INgoRah/IN10d/src/OwDevices.cpp

/* LICENSE
 *
 */
/*
 * Includes
 */
#include "Arduino.h"			 // for delayMicroseconds, digitalPinToBitMask, etc
#include <avr/pgmspace.h>
#include <avr/wdt.h>
#include "DS2482.h"
#include "OwDevices.h"

/*
 * Library class includes
 */

/*
 * Local constants
 */
#define READSCRATCH     0xBE  // Read from scratchpad
#define WRITESCRATCH    0x4E  // Write to scratchpad
#define STARTCONVO      0x44  // Tells device to take a temperature reading and put it on the scratchpad
// Scratchpad locations
#define TEMP_LSB        0
#define TEMP_MSB        1
#define HIGH_ALARM_TEMP 2
#define LOW_ALARM_TEMP  3

#if defined(AVRSIM)
uint8_t	pio_data[0x0f];
#endif

void adrGen(byte adr[8], uint8_t id);

/*
 * Objects
 */

/*
 * Local variables
 */

/*
* Function declarations
*/
void OwDevices::begin(OneWireBase *ds)
{
	ow = ds;
	ow->resetDev();
	ow->configureDev(DS2482_CONFIG_APU);
	for (int i = 0; i < MAX_BUS; i++) {
		// search devs
		for (int j = 0; j < MAX_ADR; j++) {
			pio_data[i][j] = 0xff;
			dev_vers[i][j] = 0;
		}
	}
}

void OwDevices::cacheInit()
{
	uint8_t adr[8];
	byte _data[MAX_CFG_SIZE];

	if (debug > 0) {
		Serial.println(F("Cache and Version update"));
	}
	for (int i = 0; i < MAX_BUS; i++) {
		ow->selectChannel(i);
		ow->reset_search();
		// search devs
		while (ow->search(adr)) {
			wdt_reset();
			if (adr[0] == 0x29) {
				ds2408PioGet(i, adr, true);
				if (adr[1] < MAX_ADR) {
					dev_vers[i][adr[1]] = 5;
					if (debug > 0) {
						Serial.print(i, HEX);
						Serial.print(F("."));
						Serial.println(adr[1], HEX);
					}
					ds2408CfgRead(i, adr, _data);
					dev_vers[i][adr[1]] = _data[22];
				}
			}
		}
	}
	//versionUpdate(0, 8);
	//versionUpdate(0, 2);
}

void OwDevices::adrGen(uint8_t bus, uint8_t adr[8], uint8_t id)
{
	adr[1] = id; // id selector
	adr[2] = bus;
	adr[3] = (uint8_t)~id;
	adr[4] = (uint8_t)~bus;
	if (adr[0] != 0x28 && adr[0] != 0x20) {
		/* set me up */
		adr[0] = 0x29; // type
	}
	adr[5] = 0x66;
	adr[6] = 0x77;
	adr[7] = ow->crc8 (adr, 7);
}

/* version 2 does not support long press detection
   version 7 supports own timer a dimming  via spécial 
   command C5 */
uint8_t OwDevices::getVersion(uint8_t bus, uint8_t id)
{
	return dev_vers[bus][id];
}

void OwDevices::versionUpdate(uint8_t bus, uint8_t id)
{
	byte adr[8], _data[MAX_CFG_SIZE];

	if (dev_vers[bus][id] == 0)
		/* not found */
		return;
	adrGen(bus, adr, id);
	ds2408CfgRead(bus, adr, _data);
	dev_vers[bus][id] = _data[22];
	wdt_reset();
	if (debug > 1) {
		Serial.print(bus);
		Serial.print(".");
		Serial.print(id);
		Serial.print(F(" version = "));
		Serial.println(dev_vers[bus][id]);
	}
}

/* requires bus selected already before */
uint8_t OwDevices::ds2408LatchReset(uint8_t* addr)
{
	uint8_t retry, tmp, err = 0;
	bool res;

#if defined(AVRSIM)
	return 0xAA;
#endif
	retry = LATCH_RESET_RETRY - 1;
	do {
		tmp = 0xff;
		res = ow->reset();
		if (res && ow->last_err == 0)
			ow->select(addr);
		if (ow->last_err == 0)
			ow->write (0xC3);
		if (ow->last_err == 0)
			tmp = ow->read();
		if (tmp == 0xAA)
			break;
		if (ow->last_err != 0) {
			err = ow->last_err;
		}
		if (err == 0)
			err = ow->last_err;
		delay(LATCH_RESET_RETRY - retry);
	} while (--retry > 0);
#ifdef DEBUG
	if ((err && retry == 0) || (err && debug > 0)) {
		log_time();
		Serial.print (F("latch reset err="));
		Serial.print (err);
		if (retry == 0)
			Serial.println(F(" ERR! "));
		else {
			Serial.print(F(" retry="));
			Serial.println(retry);
		}
	}
#endif
	if (retry == 0)
		return 0xff;

	return tmp;
}

/* Read DS2408 registers
 * [0] PIO Logic State
 * [1] Output latch
 * [2] Activity latch state
 * [3] Conditional search channel selection (unused)
 * [4] Conditional search polarity selection (unused)
 * [5] Status
 * [6] Status ext 1, used for press time detection
 * [7] Status ext 2
 *
 * Returns 0xaa in case of successful read and latch reset
 * Returns 0xff in case of latch reset issue
 * Returns 0 in case of bus error or timeout -> to be repeated
 * */
uint8_t OwDevices::ds2408RegRead(byte bus, uint8_t* addr, uint8_t* data, bool latch_reset)
{
	bool ret;
	uint8_t tmp, err = 0;
	uint8_t buf[3];  // Put everything in the buffer so we can compute CRC easily.

#if defined(AVRSIM)
	data[1] = 0x55;
	return 0xAA;
#endif
	uint8_t retry = REG_RETRY - 1;

	// read data registers
	buf[0] = 0xF0;    // Read PIO Registers
	buf[1] = 0x88;    // LSB address
	buf[2] = 0x00;    // MSB address
	do {
		//wdt_reset(); ??
		/* read latch */
		ret = ow->selectChannel(bus);
		if (ow->last_err == 0)
			ret = ow->reset();
		if (ret && ow->last_err == 0)
			ow->select(addr);
		if (ow->last_err == 0)
			ow->write (buf, 3);
		// 3 cmd bytes, 6 data bytes, 2 0xFF, 2 CRC16
		// 1:
		// try this: alway read not running into a watchdog
		// on the slave
		// if (ow->last_err == 0)
			ow->read (data, 10);
		/* check for valid status register */
		if (data[5] != 0xff)
			break;
		if (err == 0)
			err = ow->last_err;
		// if we got here, there is an issue and we
		// will try again
		delay(5);
	} while (--retry > 0);
	if (err) {
#ifdef DEBUG
		if (debug > 0  || retry == 0) {
			log_time();
			Serial.print(F("RegRead err="));
			Serial.print(err);
			if (retry == 0)
				Serial.println(F("ERR! "));
			else {
				Serial.print(F(" retry="));
				Serial.println(retry);
			}
		}
#endif
		if ((retry == 0 || data[5] == 0xff) && !latch_reset)
			return 0xff;
	}
	// TODO update cache here?
	pio_data[bus][addr[1] & 0x0f] = data[1];
	// clear the alarm status
	tmp = ds2408LatchReset(addr);

	return tmp;
}

/* Send channel data - currently not used */
uint8_t OwDevices::ds2408ChWrite(byte bus, uint8_t* addr, uint8_t* data, int cnt)
{
	(void)bus;
	(void)addr;
	(void)data;
	(void)cnt;
#if 0
	uint8_t r;
	int i;

	ow->selectChannel(bus);
	ow->reset();
	ow->select(addr);
	ow->write (0x5A);
	for (i = 0; i < cnt; i++) {
		ow->write (data[i]);
		r = ow->read();
		if (r != 0xAA) {
			// should be data[i] ... but the implementation seems wrong
			Serial.print(r, HEX);
		}
	}
#endif
	return 0xaa;
}

void OwDevices::toggleDs2413(byte bus, uint8_t* addr)
{
#if 0
	unsigned char pio, pion;
	int cnt = 10;

	ow->selectChannel(bus);
	do {
		ow->reset();
		ow->select(addr);
		ow->write (0xF5);
		pio = ow->read();
		if (cnt-- == 0)
			return;
	} while (((pio & 0xF) != (~(pio >> 4) & 0xF)));
	if ((pio & 2) == 0)
		pion = 3;
	else
		pion = 2;
	pion |= 0x2;
	cnt = 10;
	do {
		ow->reset();
		ow->select(addr);
		ow->write (0x5A);
		ow->write (0xFC | pion);
		ow->write (0xFF & (~(0xFC | pion)));
		pio = ow->read();
		if (cnt-- == 0)
			return;
	} while (pio != 0xAA);
#else
	(void)bus;
	(void)addr;
#endif
}

uint8_t OwDevices::ds2408PioSet(byte bus, uint8_t* addr, uint8_t pio)
{
#if defined(AVRSIM_TOP)
	pio_data[bus][addr[1] & 0x0f] = pio;
	return 0xAA;
#else
	uint8_t r, retry, err = 0;
	bool ret;

	retry = PIOSET_RETRY - 1;
	do {
		r = 0xff;
		wdt_reset();
		ret = ow->selectChannel(bus);
		if (ret)
			ret = ow->reset();
		if (ret)
			ow->select(addr);
		if (ow->last_err == 0)
			ow->write (0x5A);
		if (ow->last_err == 0)
			ow->write (pio);
		if (ow->last_err == 0)
			ow->write (0xFF & ~(pio));
		//if (ow->last_err == 0)
		// lets try a pseudo read at least to avoid
		// a hung dev
		r = ow->read();
		if (r == 0xAA)
			break;
		if (err == 0)
			err = ow->last_err;
		delay(5);
	} while (--retry > 0);
	// if err && retry > 0: err = 0
#ifdef EXT_DEBUG
	if ((err && retry == 0) || (err && debug > 0)) {
		log_time();
		Serial.print(F("PioSet "));
		Serial.print(bus);
		Serial.print(F("."));
		Serial.print(addr[1]);
		Serial.print(F(" error ="));
		Serial.print(err);
		Serial.print(F(" data="));
		Serial.print(pio, HEX);
		Serial.print(F(" r="));
		Serial.print(r, HEX);
		if (retry == 0)
			Serial.println(F(" ERR! "));
		else {
			Serial.print(F(" retry= "));
			Serial.println(retry);
		}
	}
#endif
	if (r == 0xAA) {
		// success
		ds2408LatchReset(addr);
		// TODO update cache
		pio_data[bus][addr[1] & 0x0f] = pio;
	}
	return r;
#endif
}


uint8_t OwDevices::ds2408xPinSet(byte bus, uint8_t* addr, uint8_t pio, uint8_t level, uint8_t cmd, uint8_t val)
{
	byte data[5] = { 0xC5, cmd, pio, val, level };
	uint16_t crc;
	bool ret;

	wdt_reset();
	/* if setting any level, a level 0 means stop */
	if (level == 0 && cmd == 0xDD)
		/* dim down */
		data[1] = 0xEB;
	ret = ow->selectChannel(bus);
	if (ret)
		ret = ow->reset();
	if (ret)
		ow->select(addr);
	for (int i = 0; i < 5; i++) {
		ow->write(data[i]);
		if (ow->last_err != 0)
			break;
	}
	//if (ow->last_err == 0)
	// lets try a pseudo read at least to avoid
	// a hung dev
	crc = ow->read();
	crc |= ow->read() << 8;
	uint16_t crc16 = ow->crc16(data, 5, 0);
	if (debug > 2) {
		for (int i = 0; i < 5; i++) {
			Serial.print(F(" "));
			Serial.print(data[i], HEX);
			Serial.print(F(" "));
		}
	}
	if (crc == ~crc16)
		return 0xAA;

	Serial.print(F("CRC mismatch calc="));
	Serial.println(~crc16, HEX);
	
	return 0xff;
}

/* reads and returns the Output latch state register

TODO make sure, that the data is correct ... how? */
uint8_t OwDevices::ds2408PioGet(byte bus, uint8_t* addr, uint8_t force)
{
	uint8_t res, d[10];

	if (force == 0 && pio_data[bus][addr[1] & 0x0f] != 0)
		return 	pio_data[bus][addr[1] & 0x0f];

#if defined(AVRSIM)
	return pio_data[bus][addr[1] & 0x0f];
#endif

	res = ds2408RegRead(bus, addr, d, false);
	if (res != 0xaa) {
		//Serial.print("Read error: ");
		//Serial.println(res, HEX);
	} else
		pio_data[bus][addr[1] & 0x0f] = d[1];

	return d[1];
}

/**
 * data - array of min 24 items
 */
int OwDevices::ds2408CfgRead(byte bus, byte adr[8], uint8_t* data)
{
	int i, len = MAX_CFG_SIZE;

	ow->selectChannel(bus);
	ow->reset();
	ow->select(adr);
	ow->write (0x85);

	for (i = 0; i < len - 1; i++)
		data[i] = ow->read ();

	return len;
}

void OwDevices::ds2408CfgWrite(byte bus, byte adr[8], uint8_t* d, uint8_t len)
{
	int i;

	ow->selectChannel(bus);
	ow->reset();
	ow->select(adr);
	ow->write (0x86);
	for (i = 0; i < len; i++)
		ow->write(d[i]);
}

/**
 * Returns temperature raw. celsius = tempRead * 16
 * mode 0: start conversion
 * 1: set alarms and reset
 * 2: read temperature and scratchpad
 * No retry handling because the data might not so important as next cycle
 * will come
*/
int16_t OwDevices::tempRead(byte busNr, byte addr[8], byte mode, uint8_t* hum)
{
	uint8_t scratchPad[9];
	bool ret;

	ret = ow->selectChannel(busNr);
	if (!ret)
		return -1;
	ow->reset();
	ow->select(addr);
	switch (mode) {
	case 0:
		ow->write(STARTCONVO);
		return 0;
	case 2:
		ow->write(WRITESCRATCH);
		ow->write(35); // high alarm temp
		ow->write(10); // low alarm temp
		return 0;
	case 1:
	default:
		/* read temp */
		break;
	}
	ow->write(READSCRATCH);
	// Read all registers in a simple loop
	// byte 0: temperature LSB
	// byte 1: temperature MSB
	// byte 2: high alarm temp
	// byte 3: low alarm temp
	// byte 4: DS18S20: store for crc
	//         DS18B20 & DS1822: configuration register
	// byte 5: internal use & crc
	// byte 6: DS18S20: COUNT_REMAIN
	//         DS18B20 & DS1822: store for crc
	// byte 7: DS18S20: COUNT_PER_C
	//         DS18B20 & DS1822: store for crc
	// byte 8: SCRATCHPAD_CRC
#if 0
	Serial.print(F(" "));
	for (uint8_t i = 0; i < 9; i++) {
		scratchPad[i] = ow->read();
		Serial.print(scratchPad[i], HEX);
		Serial.print(F(" "));
	}
	Serial.println();
#else
	for (uint8_t i = 0; i < 9; i++)
		scratchPad[i] = ow->read();
#endif
	int16_t raw = (scratchPad[1] << 8) | scratchPad[0];
#define cfg  (scratchPad[4] & 0x60)

	// at lower res, the low bits are undefined, so let's zero them
	if (cfg == 0x00) raw = raw & ~7;  // 9 bit resolution, 93.75 ms
	else if (cfg == 0x20) raw = raw & ~3; // 10 bit res, 187.5 ms
	else if (cfg == 0x40) raw = raw & ~1; // 11 bit res, 375 ms
	//// default is 12 bit resolution, 750 ms conversion time
	// to be done by caller if needed
  	// celsius = (float)raw / 16.0;
	if (hum != NULL)
		*hum = scratchPad[5];

	return raw;
}

int16_t OwDevices::adcRead(byte busNr, byte addr[8], byte ch, byte mode)
{
	bool ret;
	uint16_t crc, dat[4];

	ret = ow->selectChannel(busNr);
	if (!ret)
		return -1;
	ow->reset();
	ow->select(addr);
	if (mode == 0) {
		ow->write(0x3c);
		ow->write(ch);
		// clear all
		ow->write(0x55);
		crc = ow->read();
		crc |= ow->read() << 8;
		return 0;
	}
	ow->write(0xAA);
	ow->write(0x0);
	ow->write(0x0);
	for (byte i = 0; i < 4; i++) {
		dat[i] = ow->read();
		dat[i] |= ow->read() << 8;
	}
	crc = ow->read();
	crc |= ow->read() << 8;

	return dat[ch - 1];
}
