INgoRah/IN10d/src/unit_tests.cpp

/* LICENSE
 *
 */
/*
 * Includes
 */
#if ARDUINO >= 100
#include "Arduino.h"			 // for delayMicroseconds, digitalPinToBitMask, etc
#else
#include "WProgram.h"			// for delayMicroseconds
#include "pins_arduino.h"	// for digitalPinToBitMask, etc
#endif
#include <avr/sleep.h>
#include <avr/pgmspace.h>
#include "main.h"

#if defined(AVRSIM)
/*
 * Library classs includes
 */
#include <Wire.h>
#include <OneWireBase.h>
#include <DS2482.h>
#include "WireWatchdog.h"
#include "TwiHost.h"
#include "CmdCli.h"
#include "OwDevices.h"
#include "SwitchHandler.h"

extern unsigned long timer0_millis;

/*
 * Local constants
 */

/*
 * Objects
 */
extern SwitchHandler swHdl;
extern OneWireBase *ds;
extern uint8_t pio_data[0x0f];
extern OwDevices ow;

/*
 * Local variables
 */

/*
* Function declarations
*/

void testSetup() {
	Serial.begin(115200);

	Serial.print(F("One Wire Control..."));
	ow.begin(ds);

	swHdl.begin(ds);
	light = swHdl.light_thr + 1;
	PCMSK1 |= (_BV(PCINT8) | _BV(PCINT9) | _BV(PCINT10) | _BV(PCINT11));
    PCIFR |= _BV(PCIF1); // clear any outstanding interrupt
    PCICR |= _BV(PCIE1); // enable interrupt for the group
}

void testLoop()
{
	swHdl.loop();
}

void tableSetup()
{
	sw_tbl[0].src.data = 0;
	sw_tbl[0].dst.data = 0;

	// global switch #0: 0, 1, 2 for on/off type
	// dst 1 2 1
	sw_tbl[0].src.sa.bus = 0;
	sw_tbl[0].src.sa.adr = 1;
	sw_tbl[0].src.sa.latch = 2; // 2nd bit = 2
	sw_tbl[0].dst.da.bus = 1;
	sw_tbl[0].dst.da.adr = 2;
	sw_tbl[0].dst.da.pio = 1;
	// global switch #1: 0, 1, 4 for level type
	// dst 3 3 0
	sw_tbl[1].src.data = 0;
	sw_tbl[1].dst.data = 0;
	sw_tbl[1].src.sa.bus = 0;
	sw_tbl[1].src.sa.adr = 1;
	sw_tbl[1].src.sa.latch = 3; // 3rd bit, 1, 2, 4
	sw_tbl[1].dst.da.bus = 3;
	sw_tbl[1].dst.da.adr = 3;
	sw_tbl[1].dst.da.pio = 0;
	// global switch: 0, 2, 2 for on/off type
	// dst 2 1 0
	sw_tbl[2].src.data = 0;
	sw_tbl[2].dst.data = 0;
	sw_tbl[2].src.sa.bus = 0;
	sw_tbl[2].src.sa.adr = 2;
	sw_tbl[2].src.sa.latch = 2; // 3rd bit, 1, 2, 4
	sw_tbl[2].dst.da.bus = 2;
	sw_tbl[2].dst.da.adr = 1;
	sw_tbl[2].dst.da.pio = 0;

#ifdef SOFTOFF_SUPPORT
	// global timer switch (PIR): 0, 2, 4 for level type
	// dst 3 3 0
	timed_tbl[0].type = TYPE_DARK_SOFT_30S;
	timed_tbl[0].src.data = 0;
	timed_tbl[0].dst.data = 0;
	timed_tbl[0].src.sa.bus = 0;
	timed_tbl[0].src.sa.adr = 2;
	timed_tbl[0].src.sa.latch = 3; // 3rd bit = 4 (1, 2, 4)
	timed_tbl[0].dst.da.bus = 3;
	timed_tbl[0].dst.da.adr = 3;
	timed_tbl[0].dst.da.pio = 0;
#endif
	// global timer switch (PIR): 2, 2, 1 for on/off type
	// dst 2 1 0
	timed_tbl[0].type = TYPE_DARK_30S;
	timed_tbl[1].src.data = 0;
	timed_tbl[1].dst.data = 0;
	timed_tbl[1].src.sa.bus = 2;
	timed_tbl[1].src.sa.adr = 2;
	timed_tbl[1].src.sa.latch = 1;
	timed_tbl[1].dst.da.bus = 2;
	timed_tbl[1].dst.da.adr = 1;
	timed_tbl[1].dst.da.pio = 0;
/*
	dim_tbl[2].dst.da.bus = 3;
	dim_tbl[2].dst.da.adr = 3;
	dim_tbl[2].dst.da.pio = 0;
	// optional
	dim_tbl[0].dst.da.bus = 2;
	dim_tbl[0].dst.da.adr = 7;
	dim_tbl[0].dst.da.pio = 0;
*/
}

int MainTest(int test)
{
	static const byte latch = 6;
	uint8_t dadr, dpio;

	Serial.print("Test Case ");
	Serial.println(test);

	Serial.println("Test Case Setup");
	testSetup();
	tableSetup();
	swHdl.mode = MODE_ALRAM_HANDLING | MODE_AUTO_SWITCH;

	if (test == 1) {
		/*
		Case 1:
		switch #0 on (before off) - and off
		*/
		dadr = sw_tbl[0].dst.da.adr;
		dpio = 1 << sw_tbl[0].dst.da.pio;
		uint8_t mask = ~dpio;
		pio_data[dadr] = 0xff;
		/* bus, id, pio data read, mode */
		swHdl.switchHandle(0, 1, 2);
		Serial.println(pio_data[dadr], HEX);
		Serial.print(" <>");
		Serial.println(mask, HEX);
		if (pio_data[dadr] != mask)
			return __LINE__;
		Serial.println("test loop");
		testLoop();
		// off
		Serial.println("switch off");
		swHdl.switchHandle(0, 1, 2);
		if (pio_data[dadr] != 0xff)
			return __LINE__;
		testLoop();
	}
	if (test == 2) {
		/*
		Case 2:
		switch level on ... 2nd ... off
		*/
		dadr = sw_tbl[1].dst.da.adr;
		dpio = sw_tbl[1].dst.da.pio;
		pio_data[dadr] = 0x0;

		swHdl.switchHandle(0, 1, 4);
		if (pio_data[dadr] != 0x71)
			return __LINE__;
		// check 1st level
		swHdl.switchHandle(0, 1, 4);
		if (pio_data[dadr] != 0xf1)
			return __LINE__;
		// check 2nd level
		swHdl.switchHandle(0, 1, 4);
		// check off
		if (pio_data[dadr] != 0x0)
			return __LINE__;
	}
	/*
	Case 3:
	timer on and off level type
	*/
	if (test == 3) {
		// timer switch (PIR): 0, 2, 4 for level type
		// dst 3 3 0
		dadr = timed_tbl[0].dst.da.adr;
		dpio = timed_tbl[0].dst.da.pio;
		pio_data[dadr] = 0x0;

		swHdl.switchHandle(0, 2, 4);
		if (pio_data[dadr] != 0xF1)
			return __LINE__;
		timer0_millis += DEF_SECS * 1000 + 100;
		swHdl.loop();
		if (pio_data[dadr] != 0x0)
			return __LINE__;
	}

	/*
	Case 4:
	switch on + timer on (not switching)
	*/
	if (test == 4) {
		// global switch #2: 0, 2, 2 for on/off type

		// global timer switch #2 (PIR): 2, 2, 1 for on/off type
		// dst 2 1 0
		dadr = sw_tbl[2].dst.da.adr;
		dpio = sw_tbl[2].dst.da.pio;
		pio_data[dadr] = 0xff;
		// switch on
		swHdl.switchHandle(0, 2, 2);
		if (pio_data[dadr] != 0xfe)
			return __LINE__;
		// timer switch (PIR): 0, 2, 4 for level type
		// must be ignored because already switched on
		// no timer started
		swHdl.switchHandle(2, 2, 1);
		// no change!
		if (pio_data[dadr] != 0xfe)
			return __LINE__;
		timer0_millis += DEF_SECS * 1000 + 100;
		swHdl.loop();
		// no change! Timer shouldn't be running
		if (pio_data[dadr] != 0xfe)
			return __LINE__;
		// switch off
		swHdl.switchHandle(0, 2, 2);
		if (pio_data[dadr] != 0xff)
			return __LINE__;
	}
	/*
	Case 5:
	level on + timer on (not switching)
	*/
	if (test == 5) {
		dadr = sw_tbl[1].dst.da.adr;
		dpio = sw_tbl[1].dst.da.pio;
		pio_data[dadr] = 0x0;
		// switch on
		swHdl.switchHandle(0, 1, 4);
		if (pio_data[dadr] != 0x71)
			return __LINE__;
		// no try to trigger the timer
		swHdl.switchHandle(0, 2, 4);
		if (pio_data[dadr] != 0x71)
			return __LINE__;
		timer0_millis += DEF_SECS * 1000 + 1000;
		swHdl.loop();
		if (pio_data[dadr] != 0x71)
			return __LINE__;
		// switch off
		swHdl.switchHandle(0, 1, 4);
		if (pio_data[dadr] != 0xf1)
			return __LINE__;
		swHdl.switchHandle(0, 1, 4);
		if (pio_data[dadr] != 0x00)
			return __LINE__;
	}
	/*
	Case 6:
	timer on and retrigger on / timer off
	*/
	if (test == 6) {
		// timer switch (PIR): 0, 2, 4 for level type
		// dst 3 3 0
		dadr = timed_tbl[0].dst.da.adr;
		dpio = timed_tbl[0].dst.da.pio;
		timed_tbl[0].type = TYPE_DARK_30S;
		pio_data[dadr] = 0x0;

		swHdl.switchHandle(0, 2, 4);
		if (pio_data[dadr] != 0xF1)
			return __LINE__;
		timer0_millis += DEF_SECS * 500 + 100;
		swHdl.loop();
		swHdl.switchHandle(0, 2, 4);
		if (pio_data[dadr] != 0xF1)
			return __LINE__;
		timer0_millis += DEF_SECS * 500 + 100;
		swHdl.loop();
		// still on
		if (pio_data[dadr] != 0xF1)
			return __LINE__;

		timer0_millis += DEF_SECS * 500 + 100;
		swHdl.loop();
		if (pio_data[dadr] != 0xF1)
			return __LINE__;
		timer0_millis += DEF_SECS * 500 + 100;
		swHdl.loop();
		// now off
		if (pio_data[dadr] != 0x0)
			return __LINE__;
	}

	if (test == 7) {
		union pio p;

		p.da.bus = 0;
		p.da.adr = 9;
		p.da.pio = 3;
		p.da.type = 2;
		// convert?
		swHdl.switchLevel(p, 100);
		swHdl.switchLevel(p, 0);

		timed_tbl[0].src.data = 0;
		timed_tbl[0].src.sa.bus = 1;
		timed_tbl[0].src.sa.adr = 3;
		timed_tbl[0].src.sa.latch = latch;
		timed_tbl[0].dst.data = 0;
		timed_tbl[0].dst.da.adr = 7;
		timed_tbl[0].dst.da.bus = 2;
		timed_tbl[0].dst.da.pio = 1;
		dim_tbl[0].dst.data = timed_tbl[0].dst.data;
		/*
		swHdl.switchHandle(1, 3, (1 << (latch - 1)), (320 / 32), MODE_ALRAM_HANDLING | MODE_ALRAM_POLLING | MODE_AUTO_SWITCH);
		swHdl.switchHandle(1, 3, (1 << (latch - 1)), (320 / 32), MODE_ALRAM_HANDLING | MODE_ALRAM_POLLING | MODE_AUTO_SWITCH);
		swHdl.switchHandle(1, 3, (1 << (latch - 1)), (320 / 32), MODE_ALRAM_HANDLING | MODE_ALRAM_POLLING | MODE_AUTO_SWITCH);
		swHdl.switchHandle(1, 3, (1 << (latch - 1)), (320 / 32), MODE_ALRAM_HANDLING | MODE_ALRAM_POLLING | MODE_AUTO_SWITCH);
		swHdl.switchHandle(1, 3, (1 << (latch - 1)), (320 / 32), MODE_ALRAM_HANDLING | MODE_ALRAM_POLLING | MODE_AUTO_SWITCH);
		*/
	}
	if (test == 8) {
		union d_adr_8 dst;
		union pio p;

		p.da.bus = 0;
		p.da.adr = 9;
		p.da.pio = 0;
		p.da.type = 2;
		swHdl.switchLevel(p, 15);

		dst.da.bus = 0;
		dst.da.adr = 9;
		dst.da.pio = 0;
		swHdl.actorHandle(dst, ON);

		swHdl.actorHandle(dst, TOGGLE);
	}
	/*
	Case 9:
	timer on and soft off, level type
	*/
	if (test == 9) {
		// timer switch (PIR): 0, 2, 4 for level type
		// dst 3 3 0
		dadr = timed_tbl[0].dst.da.adr;
		dpio = timed_tbl[0].dst.da.pio;
		timed_tbl[0].type = TYPE_DARK_30S;
		pio_data[dadr] = 0x0;

		swHdl.mode = MODE_ALRAM_HANDLING | MODE_AUTO_SWITCH;
		swHdl.switchHandle(0, 2, 4);
		if (pio_data[dadr] != 0xF1)
			return __LINE__;
		timer0_millis += 25 * 1000 + 100;
		swHdl.loop();
		// 26
		timer0_millis += 1000;
		swHdl.loop();
		// 29
		timer0_millis += 3000;
		swHdl.loop();
		timer0_millis += 1000;
		// off
		swHdl.loop();

		/* this is off!
		timer0_millis += DEF_SECS * 1000 + 100;
		swHdl.loop();
		*/
		if (pio_data[dadr] != 0x0)
			return __LINE__;
	}
	/*
	Case 10:
	simple pin change event
	*/
	if (test == 10) {
		byte pinSignal;
		static uint8_t pind_old = _BV(PD4);
		uint8_t pind;

		/* just check for changes pd7 to high */
		/* report on change to high level */
		pind = (_BV(PD4) | _BV(PD7));
		Serial.print(pind, HEX);
		if (pind & _BV(PD7) && (pind_old & _BV(PD7)) == 0)
			pinSignal |= 0x4;
		Serial.print(pinSignal, HEX);
		pind_old = _BV(PD4) | _BV(PD7);
		// pd7 goes to low
		pind = _BV(PD4);
		Serial.print(pind, HEX);
		if (pind & _BV(PD7) && (pind_old & _BV(PD7)) == 0)
			pinSignal |= 0x4;
		Serial.print(pinSignal, HEX);
		pind_old = _BV(PD4);

		// pd4 goes low
		pind = 0;
		//pind = 0 & ~pind_old;
		Serial.print(pind, HEX);
		/* report on change to low level */
		if (((pind & _BV(PD4)) == 0) && (pind_old & _BV(PD4)))
			pinSignal |= 0x2;
		Serial.print(pinSignal, HEX);
	}
	return 0;
}

uint8_t atoh(const char *str, uint8_t offset = 0)
{
	uint8_t b, lo;

	b = toupper(str[offset++]);
	if (isxdigit(b))
	{
		if (b > '9')
			// software offset for A-F
			b -= 7;
		// subtract ASCII offset
		b -= 0x30;
		lo = toupper(str[offset]);
		if (lo != 0 && isxdigit(lo))
		{
			b = b << 4;
			if (lo > '9')
				lo -= 7;
			lo -= 0x30;
			b = b + lo;
		}
		return b;
	}

	return 0;
}

int main()
{
	int ret = 0, i;
#if 0
	uint8_t bit = digitalPinToBitMask(5);
	Serial.print(bit);
	analogWrite(5, 100);
#endif
	debug = 4;
	light = 220;
	for (i = 1; i < 8; i++)
	{
		ret = MainTest(i);
		if (ret) {
			Serial.print("FAIL in ");
			Serial.println(ret);
		}
	}
	return ret;
}
#endif /* AVRSIM */
